jtsiomb/nixiedisp/fw/src/timer.c

#include <avr/io.h>
#include <avr/interrupt.h>

unsigned long nticks;
int timer_running;

void timer_init(void)
{
	/* 230 / (14745600 / 64) is very close to 1ms */
	TCCR0A = 2;	/* mode 2: CTC */
	TCCR0B = 3;	/* clk/64 */
	OCR0A = 229;
	TIMSK0 = 0;	/* disable interrupt by default, enable on start */

	nticks = 0;
	timer_running = 0;
}

void timer_start(void)
{
	TIMSK0 = 2;	/* enable output compare match A interrupt */
	timer_running = 1;
}

void timer_stop(void)
{
	TIMSK0 = 0;	/* stop the interrupts */
	timer_running = 0;
}

void timer_reset(void)
{
	cli();
	nticks = 0;
	TCNT0 = 0;
	sei();
}

ISR(TIMER0_COMPA_vect)
{
	++nticks;
}
