jtsiomb/nixiedisp/sw/nixiedisp-gui/src/main.cc

/*
nixiedisp-gui - settings and control app for the nixie tube display
Copyright (C) 2021  John Tsiombikas <nuclear@member.fsf.org>

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
You should have received a copy of the GNU General Public License
along with this program.  If not, see <http://www.gnu.org/licenses/>.
*/
#include <QApplication>
#include "mainwin.h"

QWidget *mainwin;

int main(int argc, char **argv)
{
	QCoreApplication::setApplicationName("nixiedisp-gui");

	QApplication app(argc, argv);
	MainWin w;
	w.show();

	mainwin = &w;

	return app.exec();
}
